jlschaper/ERCT/ERCT_Buffer_V3/Assets/IMG_6648 Small.png

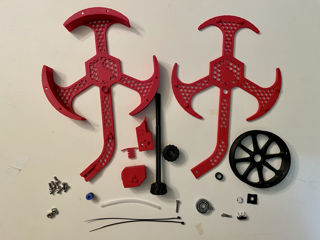
ERCT_Buffer_V3/Assets/IMG_6648 Small.png
