jlschaper/ERCT/ERCT_Buffer_V3/Assets/IMG_6662 Small.png

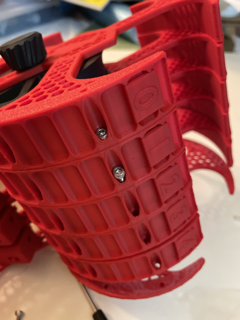
ERCT_Buffer_V3/Assets/IMG_6662 Small.png
