jlschaper/ERCT/ERCT_Buffer_V3/Assets/IMG_6675 Small.png

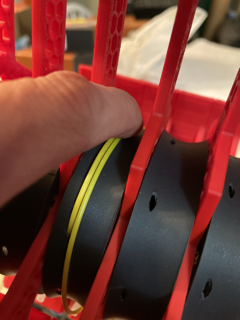
ERCT_Buffer_V3/Assets/IMG_6675 Small.png
