jlschaper/ERCT/ERCT_Buffer_V3/User_Mods/Wolffy01/625_Mod_5mm_Tread/Stls/625 case.stl

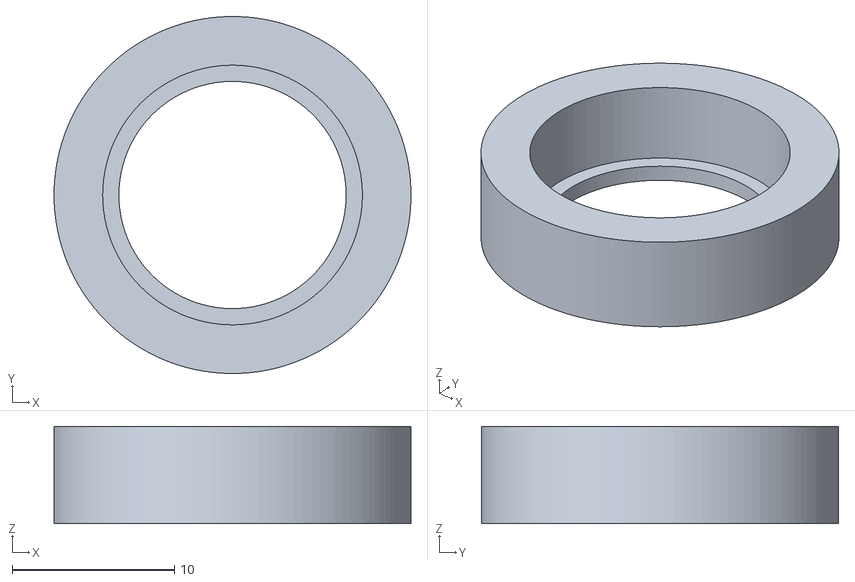
[picture p49: CAD file, 2025-10-11]
ERCT_Buffer_V3/User_Mods/Wolffy01/625_Mod_5mm_Tread/Stls/625 case.stl
22.0 x 22.0 x 6.00
