jlschaper/ERCT/CottonTail_Lite/Runout_Buffer_Arm_Mount_xN.stl

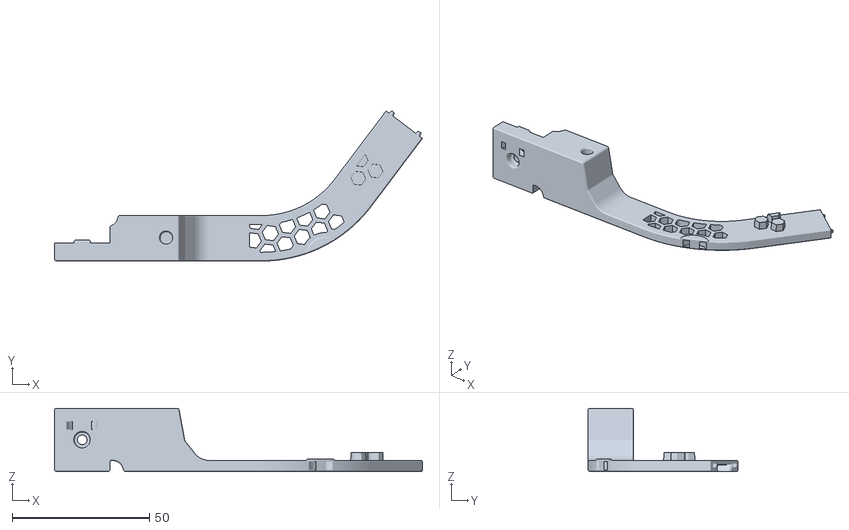
[picture p50: CAD file, 2025-10-11]
CottonTail_Lite/Runout_Buffer_Arm_Mount_xN.stl
134.3 x 54.8 x 23.1
