jlschaper/ERCT/ERCT_Buffer_V3/Options/[a]_Arm_Anchor_PTFE.stl

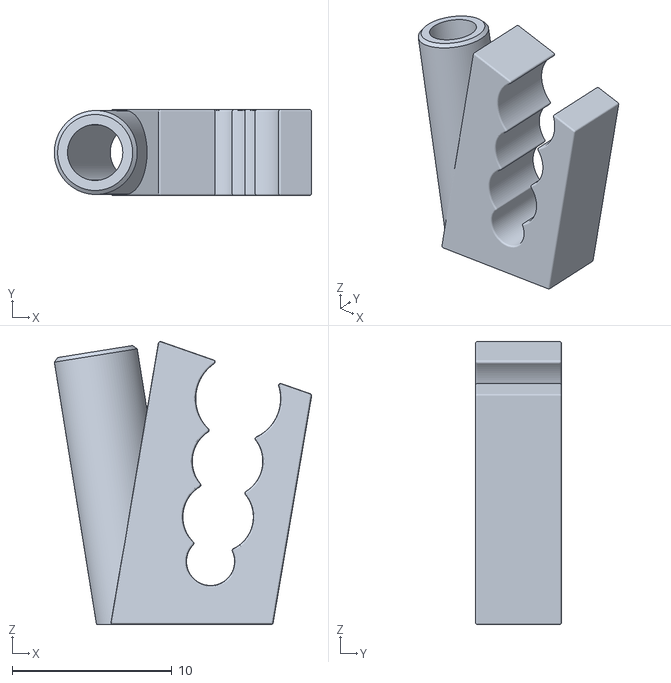
[picture p51: CAD file, 2025-10-11]
ERCT_Buffer_V3/Options/[a]_Arm_Anchor_PTFE.stl
16.1 x 5.38 x 17.7
