jlschaper/ERCT/ERCT_Buffer_V3/Rev2/Buffer_Wheel/Crank.stl

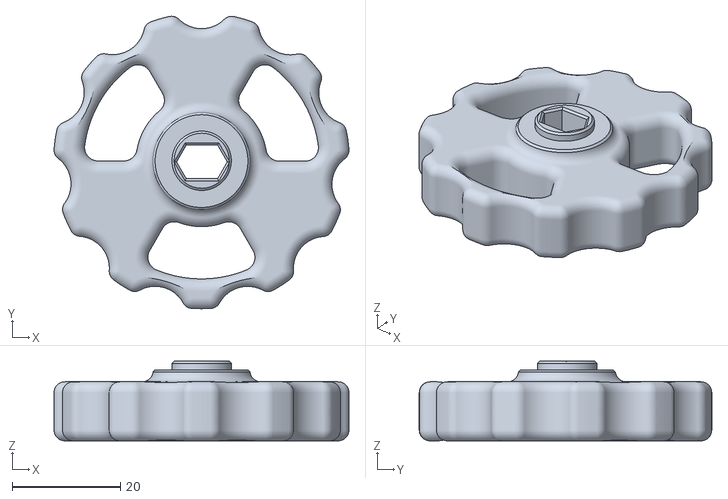
[picture p53: CAD file, 2025-10-11]
ERCT_Buffer_V3/Rev2/Buffer_Wheel/Crank.stl
54.4 x 53.9 x 14.7
