jlschaper/ERCT/ERCT_Buffer_V3/Rev2/end_cap+electronics/End_Cap_Mount.stl

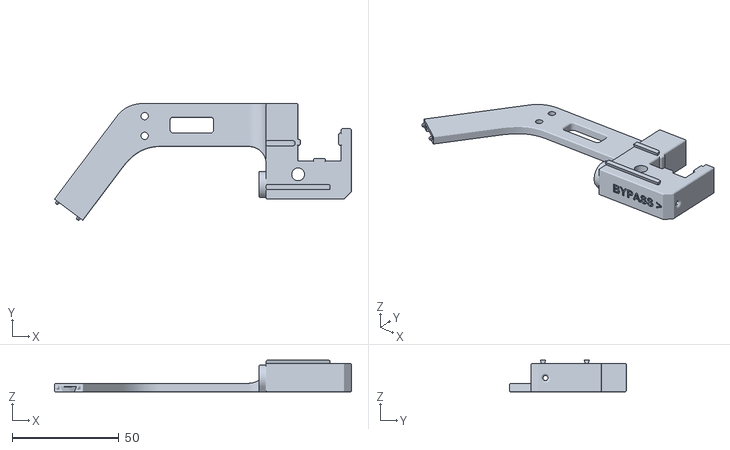
[picture p54: CAD file, 2025-10-11]
ERCT_Buffer_V3/Rev2/end_cap+electronics/End_Cap_Mount.stl
139.1 x 54.7 x 14.9
