jlschaper/ERCT/ERCT_Buffer_V3/Rev2/Support_Arms/[a]Arm_Mount_xN.stl

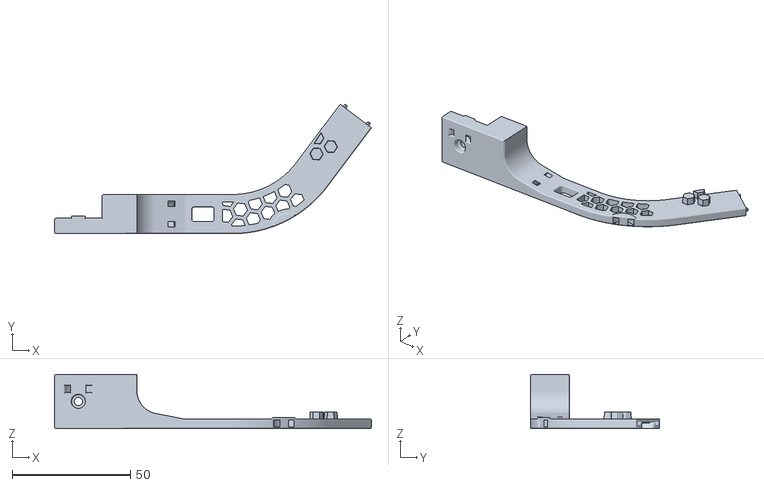
[picture p55: CAD file, 2025-10-11]
ERCT_Buffer_V3/Rev2/Support_Arms/[a]Arm_Mount_xN.stl
134.2 x 54.8 x 23.1
