jlschaper/ERCT/ERCT_Buffer_V3/User_Mods/Wolffy01/625_Mod_5mm_Tread/Stls/5mm_Arm_End_Cap.stl

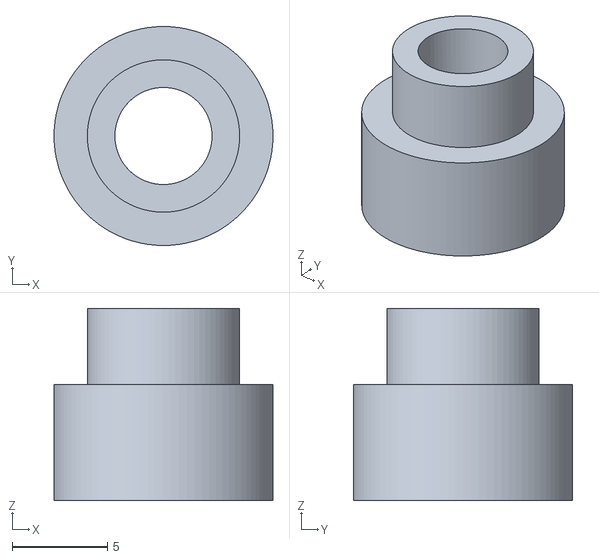
[picture p56: CAD file, 2025-10-11]
ERCT_Buffer_V3/User_Mods/Wolffy01/625_Mod_5mm_Tread/Stls/5mm_Arm_End_Cap.stl
11.5 x 11.5 x 10.1
