jlschaper/ERCT/CottonTail_Lite/Runout_Buffer_Arm_End_Cap.stl

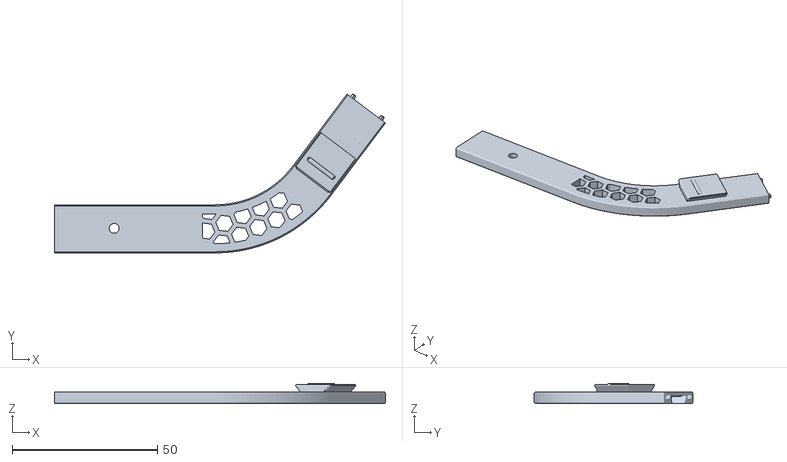
[picture p57: CAD file, 2025-10-11]
CottonTail_Lite/Runout_Buffer_Arm_End_Cap.stl
114.0 x 54.7 x 7.00
