jlschaper/ERCT/ERCT_Buffer_V3/Rev2/Axle/Axle_double_thread_9_gates.stl

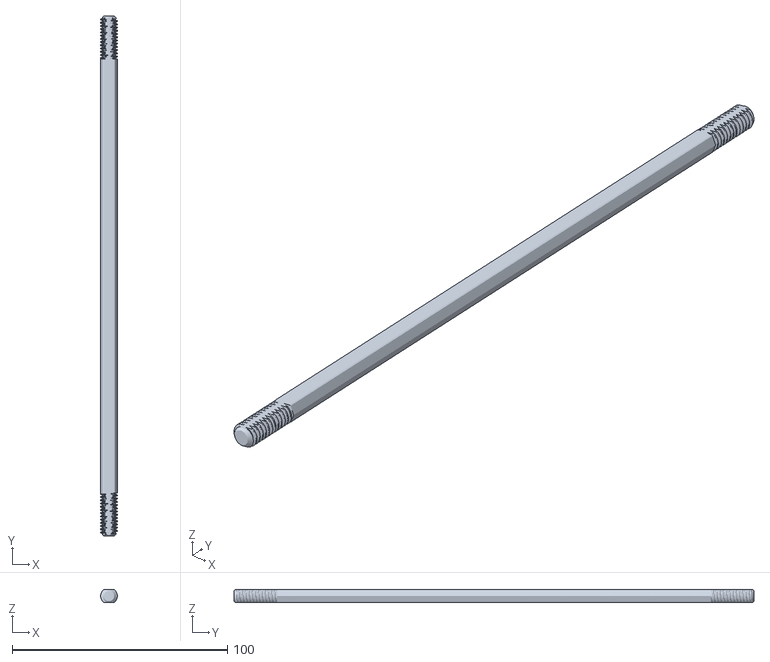
[picture p58: CAD file, 2025-10-11]
ERCT_Buffer_V3/Rev2/Axle/Axle_double_thread_9_gates.stl
7.90 x 241.8 x 5.94
