jlschaper/ERCT/ERCT_Buffer_V3/Rev2/end_cap+electronics/Universal_Box_Lid_V3.stl

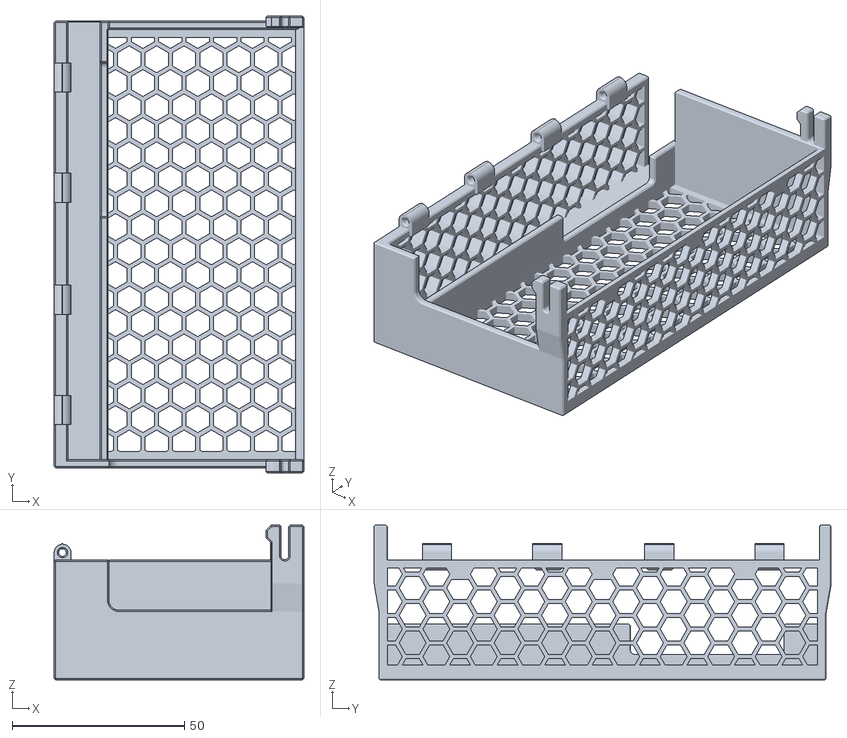
[picture p59: CAD file, 2025-10-11]
ERCT_Buffer_V3/Rev2/end_cap+electronics/Universal_Box_Lid_V3.stl
72.5 x 132.7 x 45.0
