jlschaper/ERCT/ERCT_Buffer_V3/Rev2/Support_Arms/[a]Bufferwall_inlet_xN.stl

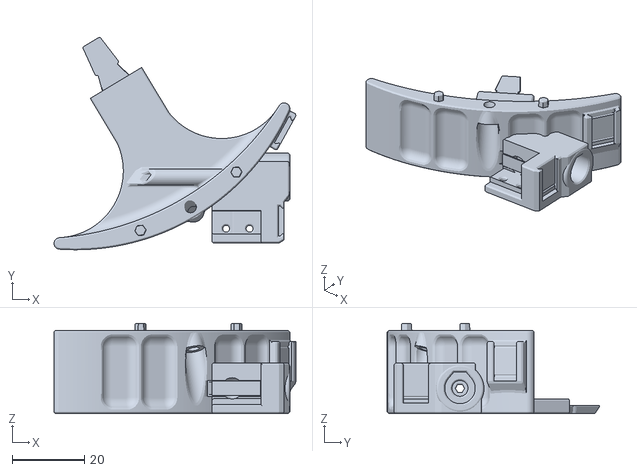
[picture p60: CAD file, 2025-10-11]
ERCT_Buffer_V3/Rev2/Support_Arms/[a]Bufferwall_inlet_xN.stl
67.1 x 58.9 x 25.0
