jlschaper/ERCT/ERCT_Buffer_V3/User_Mods/Wolffy01/625_Mod_5mm_Tread/Stls/625 case end cap.stl

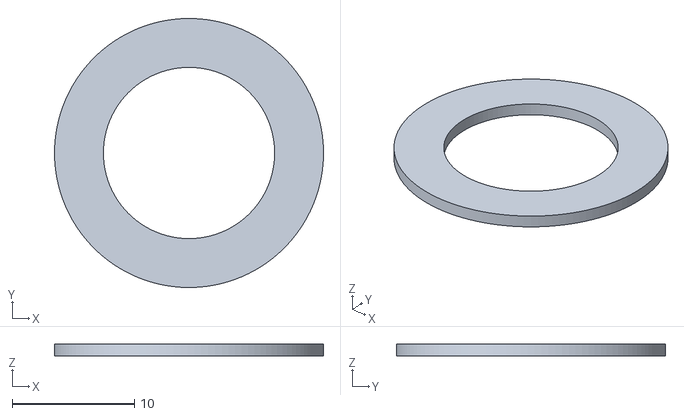
[picture p61: CAD file, 2025-10-11]
ERCT_Buffer_V3/User_Mods/Wolffy01/625_Mod_5mm_Tread/Stls/625 case end cap.stl
22.0 x 22.0 x 1.00
