jlschaper/ERCT/CottonTail_Lite/Runout_Buffer_Coupler_Block_xN.stl

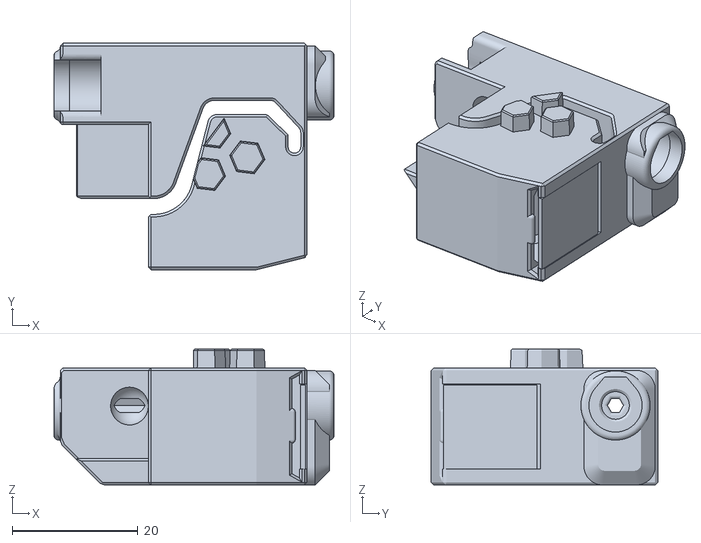
[picture p62: CAD file, 2025-10-11]
CottonTail_Lite/Runout_Buffer_Coupler_Block_xN.stl
44.5 x 36.0 x 21.6
