jlschaper/ERCT/ERCT_Buffer_V3/Rev2/Axle/Axle_double_thread_8_gates.stl

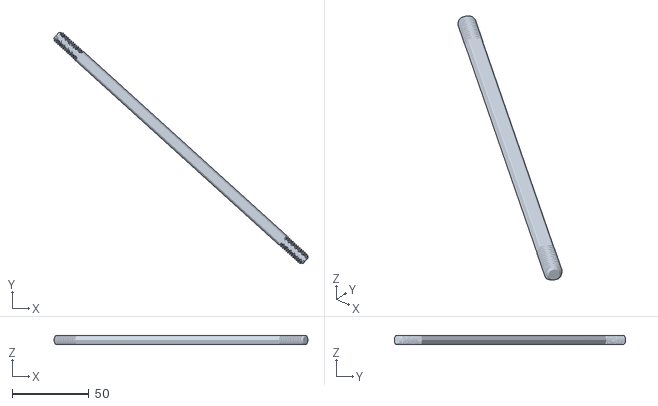
[picture p63: CAD file, 2025-10-11]
ERCT_Buffer_V3/Rev2/Axle/Axle_double_thread_8_gates.stl
165.3 x 150.7 x 5.94
