jlschaper/ERCT/ERCT_Buffer_V3/Rev2/end_cap+electronics/[a]_End_Cap_Bufferwall_V3_x2N.stl

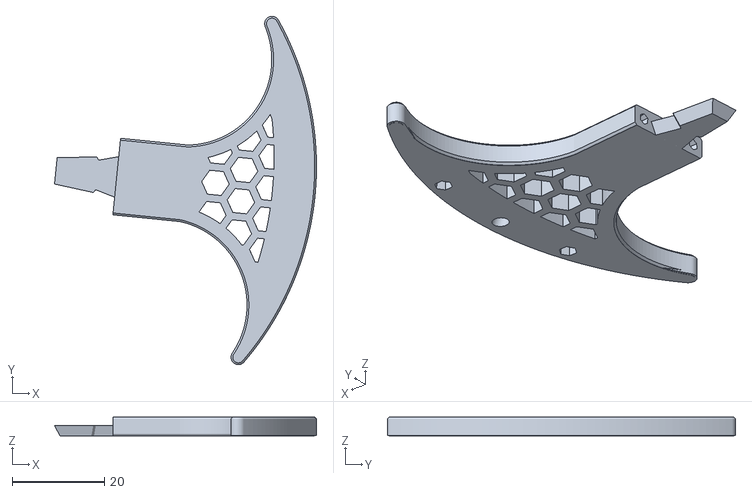
[picture p64: CAD file, 2025-10-11]
ERCT_Buffer_V3/Rev2/end_cap+electronics/[a]_End_Cap_Bufferwall_V3_x2N.stl
56.7 x 75.4 x 4.07
