jlschaper/ERCT/ERCT_Buffer_V3/Rev2/Support_Arms/Secondary_buffer_wall_x2_xN.stl

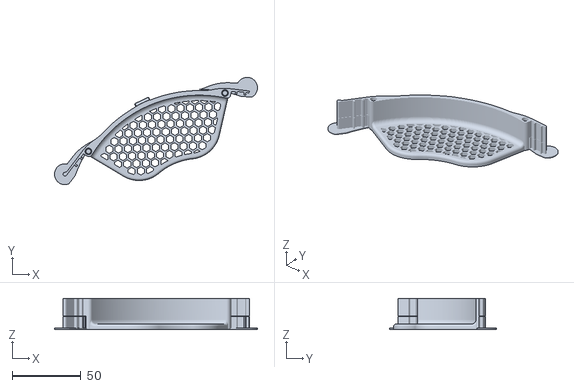
[picture p65: CAD file, 2025-10-11]
ERCT_Buffer_V3/Rev2/Support_Arms/Secondary_buffer_wall_x2_xN.stl
147.8 x 78.1 x 22.6
