jlschaper/ERCT/ERCT_Buffer_V3/User_Mods/Wolffy01/625_Mod_5mm_Tread/Stls/625 center spacer.stl

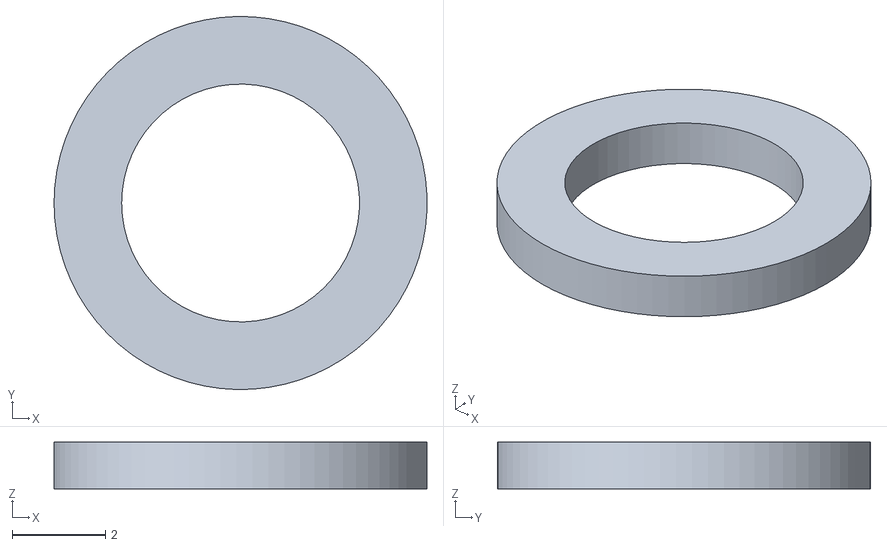
[picture p66: CAD file, 2025-10-11]
ERCT_Buffer_V3/User_Mods/Wolffy01/625_Mod_5mm_Tread/Stls/625 center spacer.stl
8.00 x 8.00 x 1.00
