jlschaper/ERCT/CottonTail_Lite/End_Arm_Cap_Mount.stl

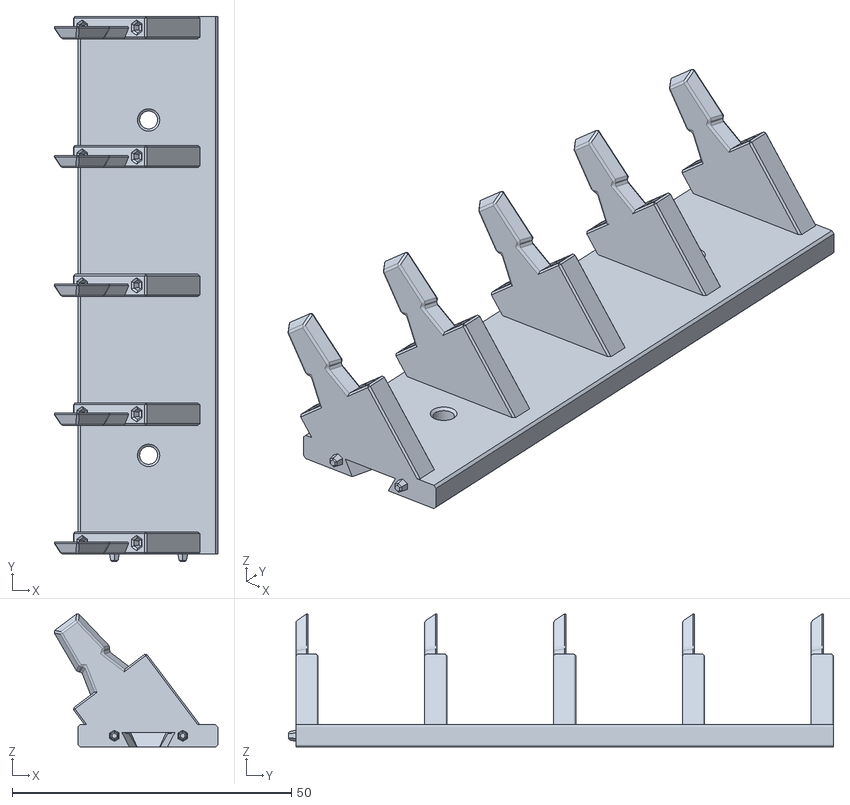
[picture p67: CAD file, 2025-10-11]
CottonTail_Lite/End_Arm_Cap_Mount.stl
29.3 x 97.5 x 23.8
