jlschaper/ERCT/ERCT_Buffer_V3/Rev2/end_cap+electronics/End_Cap_Hub_V3_xN.stl

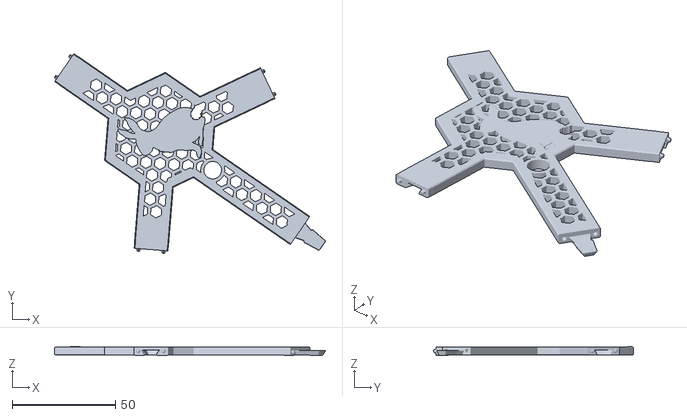
[picture p68: CAD file, 2025-10-11]
ERCT_Buffer_V3/Rev2/end_cap+electronics/End_Cap_Hub_V3_xN.stl
131.4 x 96.9 x 4.13
