jlschaper/ERCT/ERCT_Buffer_V3/User_Mods/Wolffy01/625_Mod_5mm_Tread/Stls/spacer.stl

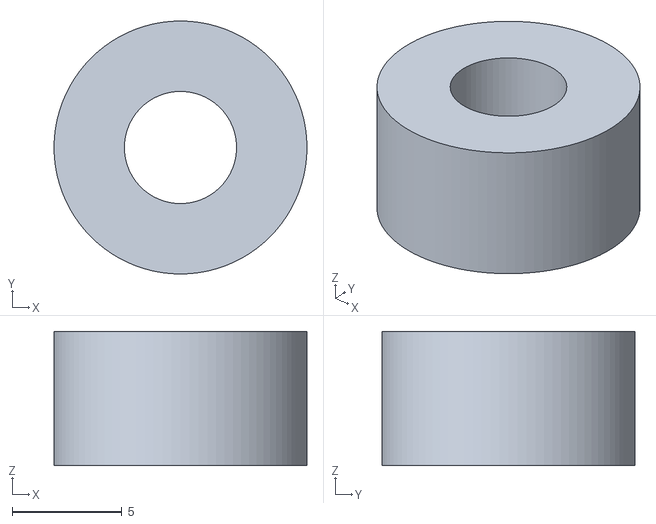
[picture p69: CAD file, 2025-10-11]
ERCT_Buffer_V3/User_Mods/Wolffy01/625_Mod_5mm_Tread/Stls/spacer.stl
11.5 x 11.5 x 6.10
