jlschaper/ERCT/ERCT_Buffer_V3/Rev2/end_cap+electronics/End_Cap_Secondary_Wall_x2N.stl

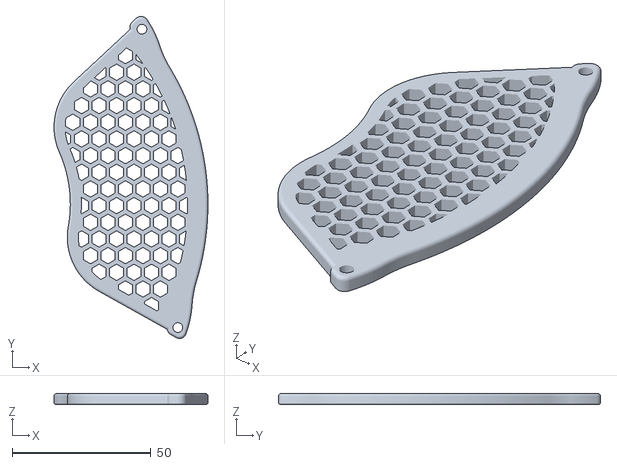
[picture p70: CAD file, 2025-10-11]
ERCT_Buffer_V3/Rev2/end_cap+electronics/End_Cap_Secondary_Wall_x2N.stl
55.4 x 115.9 x 4.00
