jlschaper/ERCT/ERCT_Buffer_V3/User_Mods/Wolffy01/625_Mod_5mm_Tread/Build_Pics/step 1.jpg

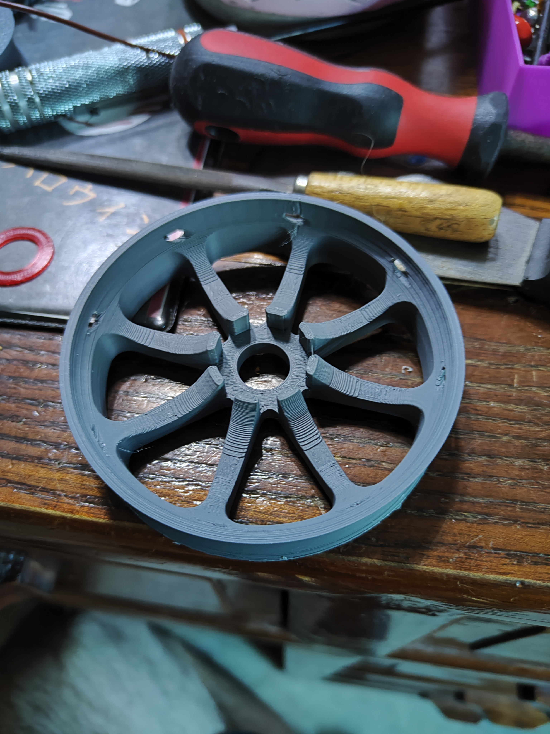
ERCT_Buffer_V3/User_Mods/Wolffy01/625_Mod_5mm_Tread/Build_Pics/step 1.jpg
